jellewie/Arduino-Smart-light/Images/Desk clock hours.jpeg

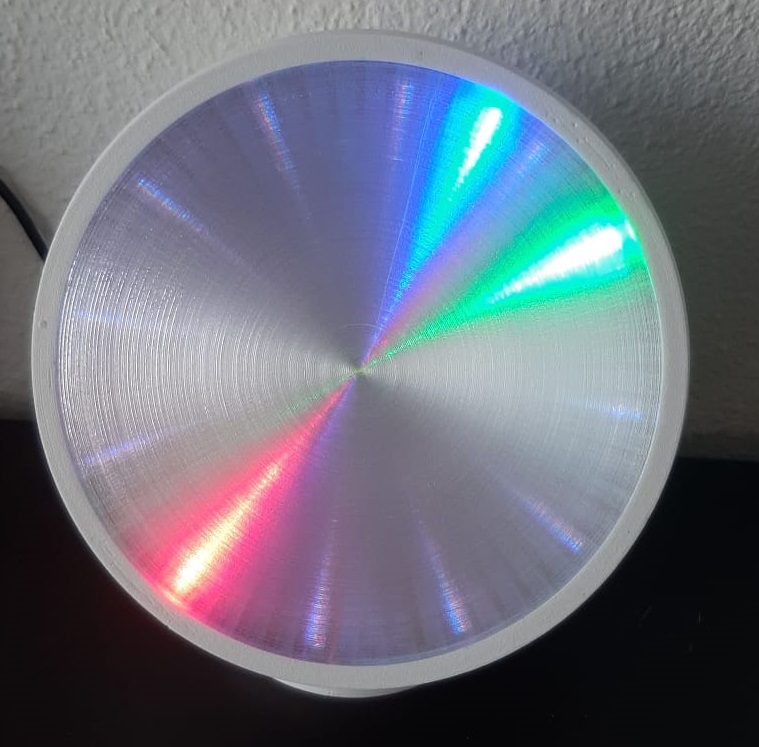
Images/Desk clock hours.jpeg
