jellewie/Arduino-Smart-light/Schematic PCB/V1.3 Desk PCB.png

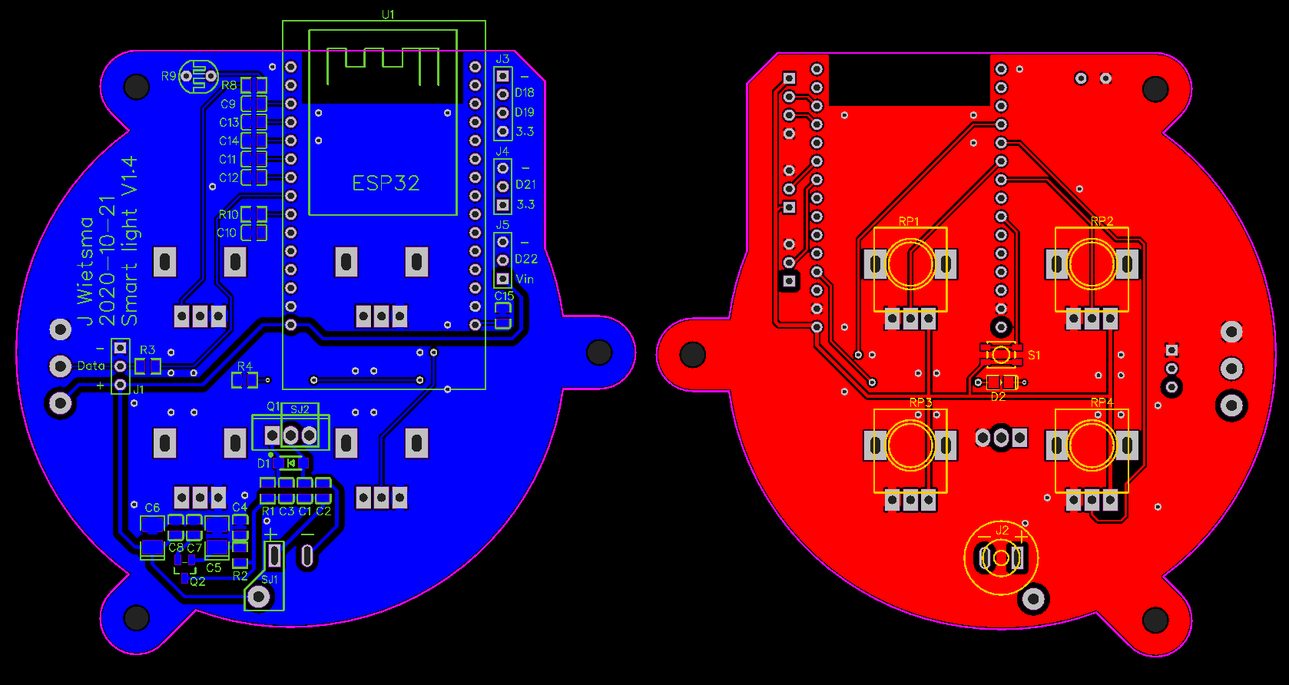
Schematic PCB/V1.3 Desk PCB.png
