jellewie/Arduino-Smart-light/Schematic PCB/V1.3 Schematic.png

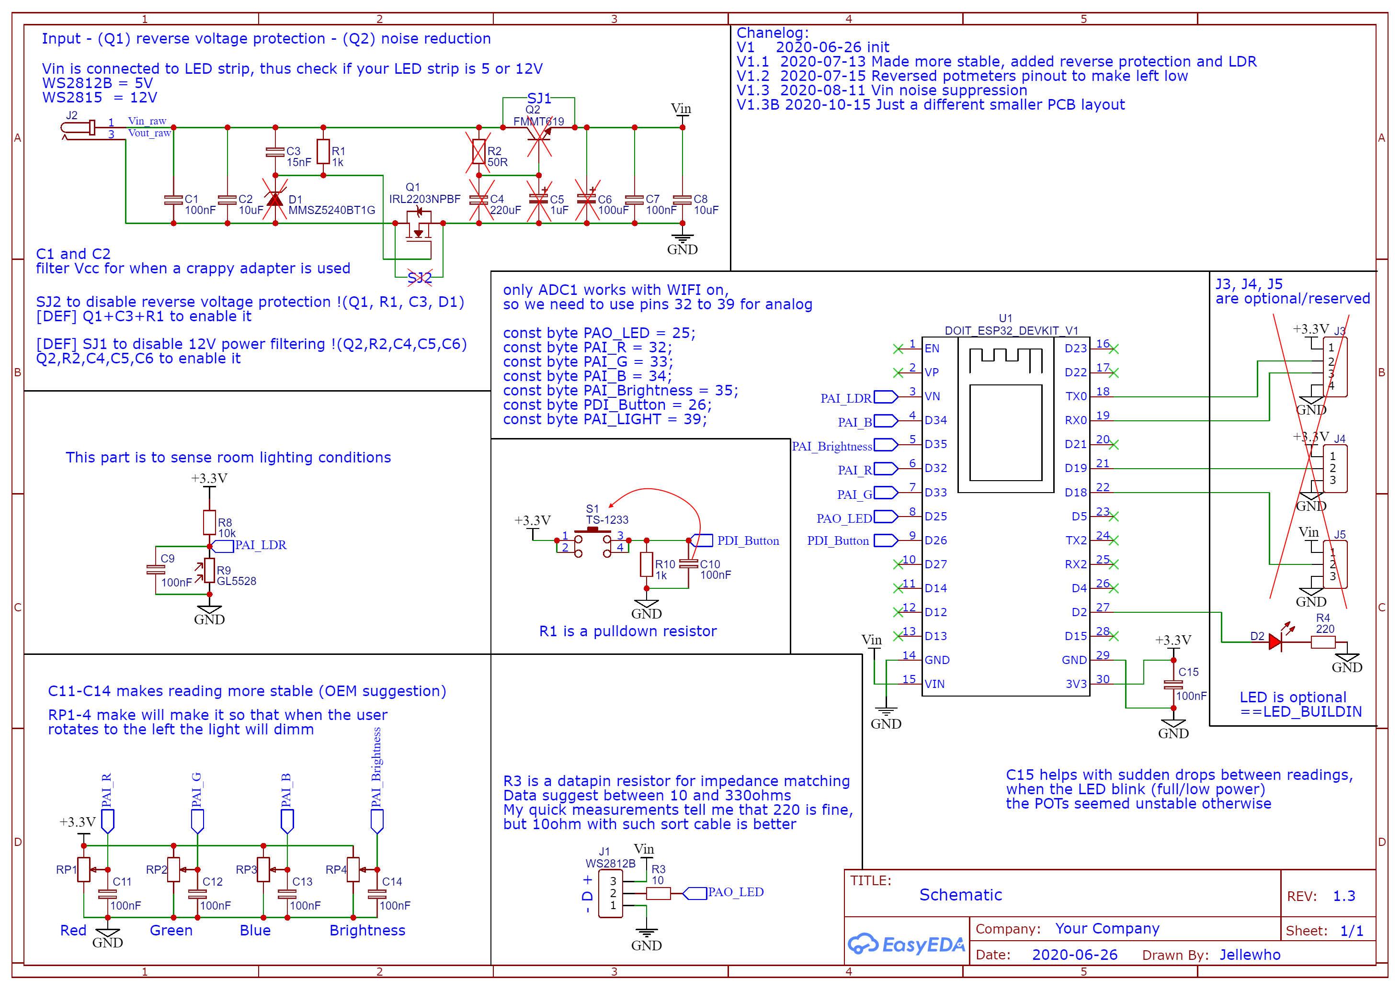
Schematic PCB/V1.3 Schematic.png
