jellewie/Arduino-Smart-light/Arduino/Task.h

/* Written by JelleWho https://github.com/jellewie
  On loop() execute         ExecuteTask()

  HOW TO ADD CUSTOM TASKS
  -"enum xxx"      Add the name to the enum to make the code better to read
  -"TaskString[]"  ^
  -DoTask()        Add what this task does
  -VarCompress()   Add things to compress the 'Var' [Optional but highly suggested)
  -VarDecompress() Add things to decomppress again, requires if Var Compression is used

  Time based tasks will not be auto deleted (execte X at HH:MM:SS)
  Delay based tasks will be auto deleted (execte X in Y ticks)
*/

#define TaskLimit 16                                            //Defined as an byte in for loops, (255 at max), Note this is hooked into WiFimanager EEPROM settings, updating from git after changing this value is NOT recommened
//#define Task_SerialEnabled
#define EEPROMSaveDelayMS 30000                                 //Save to EEPROM in X ms
enum {NONE, SWITCHMODE, DIMMING, BRIGHTEN, RESETESP, CHANGERGB, SAVEEEPROM, SYNCTIME, AUTOBRIGHTNESS, HOURLYANIMATIONS, RANDOMANIMATION}; //Just to make the code easier to read
String TaskString[] = {"NONE", "SWITCHMODE", "DIMMING", "BRIGHTEN", "RESETESP", "CHANGERGB", "SAVEEEPROM", "SYNCTIME", "AUTOBRIGHTNESS", "HOURLYANIMATIONS", "RANDOMANIMATION"}; //ALL CAPS!

const byte Task_Amount = sizeof(ModesString) / sizeof(ModesString[0]); //Why filling this in if we can automate that? :)

//<ip>/task[?PreFix=Value][&....]                               //These are currently HARDCODED into the HTML page, so shouldn't be changed if you want to use the webpage
#define PreFixMode  "o"                                         //1=TASK_ADD, 2=TASK_REMOVE
#define PreFixID    "i"                                         //Task Type (or ID for remove task)
#define PreFixVar   "a"                                         //Task Variable
#define PreFixTimeH "h"                                         //On which time the task needs to be executed
#define PreFixTimeM "m"                                         //^
#define PreFixTimeS "s"                                         //^
#define PreFixTimeT "t"                                         //In howmany ticks the task needs to be executed

struct TASK {
  byte Type = 0;                                                //The ID of the task, these are defined in the enum
  TimeS ExectuteAt = {0, 0, 0, 0};                              //The time in {HH:MM:SS:or millis} to execute this task
  String Var = "";                                              //Used for some special variables
  bool Executed = false;                                        //Just here to keep track of it a Time based task has been executed today
};
TASK TaskList[TaskLimit];
enum {TASK_NOTGIVEN, TASK_ADD, TASK_REMOVE};                    //These are commando's for PreFixMode

//Declare some functions here, so we can cross reference then in the code. Basically just placeholders to the compiler does not whine about that they do not exist yet
extern String ConvertTaskIDToString(byte IN);
extern int    ConvertTaskIDToInt(String IN);
extern void   CutVariable(String _Input, String *_Variable, byte _VariableLength);
extern bool   AddTask(TASK Item, bool _Reversed = false);
//From extern sources
extern bool   UpdateTime();

bool DoTask(TASK Item) {
  bool returnValue = true;
#ifdef Task_SerialEnabled
  Serial.print("TK: DoTask " + ConvertTaskIDToString(Item.Type) + " var=" + String(Item.Var));
  if (Item.ExectuteAt.Ticks > 0)
    Serial.println(" due to Ticks, scheduled for " + String(Item.ExectuteAt.Ticks) + " now=" + String(millis()));
  else
    Serial.println(" due to Time, scheduled for " + String(Item.ExectuteAt.HH) + ":" + String(Item.ExectuteAt.MM) + ":" + String(Item.ExectuteAt.SS));
#endif //Task_SerialEnabled
  switch (Item.Type) {
    case SWITCHMODE: {
        //Var = New Mode
        Mode = ConvertModeToInt(Item.Var);
        UpdateLEDs = true;
      } break;
    case DIMMING: {
        //Var = Stepsize,GoTo,TimeInterfall in ms
        String _Vars[3];
        CutVariable(Item.Var, &_Vars[0], 3);
        byte Stepsize = constrain(_Vars[0].toInt(), 0, 255);
        byte GoTo     = constrain(_Vars[1].toInt(), 0, 255);
        int TimeInterfall       = _Vars[2].toInt();
        byte BRI = FastLED.getBrightness();
        if (BRI - Stepsize < GoTo) {
          BRI = GoTo;
        } else {
          BRI = BRI - Stepsize;
          if (TimeInterfall > 0) {                              //If we need to go further, and need to create another task
            TASK TempTask = Item;
            TempTask.ExectuteAt.Ticks = millis() + TimeInterfall;
            AddTask(TempTask, true);
          }
        }
        FastLED.setBrightness(BRI);
        UpdateLEDs = true;
      } break;
    case BRIGHTEN: {
        //Var = Stepsize,GoTo,TimeInterfall in ms
        String _Vars[3];
        CutVariable(Item.Var, &_Vars[0], 3);
        byte Stepsize = constrain(_Vars[0].toInt(), 0, 255);
        byte GoTo     = constrain(_Vars[1].toInt(), 0, 255);
        int TimeInterfall       = _Vars[2].toInt();
        byte Now = FastLED.getBrightness();
        byte To = 255;
        if (GoTo > 0) To = GoTo;
        if (To - Now < Stepsize) {
          Now = To;
        } else {
          Now += Stepsize;
          if (TimeInterfall > 0) {
            TASK TempTask = Item;
            TempTask.ExectuteAt.Ticks = millis() + TimeInterfall;
            AddTask(TempTask, true);
          }
        }
#ifdef Task_SerialEnabled
        Serial.println("TK: BRIGHTEN from " + String(FastLED.getBrightness()) + " to " + String(Now));
#endif //Task_SerialEnabled
        FastLED.setBrightness(Now);
        UpdateLEDs = true;
      } break;
    case RESETESP: {
        ESP.restart();
      } break;
    case CHANGERGB: {
        //Var = new Red value,new Green value,new Blue value
        String _Vars[4];
        CutVariable(Item.Var, &_Vars[0], 4);
        byte GoToR = constrain(_Vars[0].toInt(), 0, 255);
        byte GoToG = constrain(_Vars[1].toInt(), 0, 255);
        byte GoToB = constrain(_Vars[2].toInt(), 0, 255);
        byte GoToL = constrain(_Vars[3].toInt(), 0, 255);
        Mode = ON;
        LastMode = Mode;
        fill_solid(&(LEDs[0]), TotalLEDs, CRGB(GoToR, GoToG, GoToB));
        if (GoToL != 0)
          FastLED.setBrightness(GoToL);
        UpdateLEDs = true;
      } break;
    case SAVEEEPROM: {
        WiFiManager.WriteEEPROM();
      } break;
    case SYNCTIME: {
        UpdateTime();                                           //Get a new sync timestamp from the server
      } break;
    case AUTOBRIGHTNESS: {
        AutoBrightness = IsTrue(Item.Var);
      } break;
    case HOURLYANIMATIONS: {
        HourlyAnimationS = constrain(Item.Var.toInt(), 0, 255);
      } break;
    case RANDOMANIMATION: {
        //Var = AnimationShowTime where 0=HourlyAnimationS
        int AnimationShowTime = Item.Var.toInt();
        if (AnimationShowTime == 0) AnimationShowTime = HourlyAnimationS;
        StartAnimation(random8(0, TotalAnimations), AnimationShowTime); //Start a random Animation
      } break;
    default:
      returnValue = false;
      break;
  }
  return returnValue;
}
String VarCompress(byte ID, String IN) {
  //Just for compression for EEPROM
#ifdef Convert_SerialEnabled
  Serial.println("CV: VarDecompress '" + String(IN) + "'");
#endif //Convert_SerialEnabled
  IN.replace("\"", "'");                                        //Make sure to change char(") since we can't use that, change to char(')
  IN.replace("\\", "/");                                        //Make sure to change char(\) since we can't use that, change to char(/)
  switch (ID) {
    case NONE: {
        return "";                                              //We do not use it, clear it so save space
      } break;
    case SWITCHMODE: {
        return String(ConvertModeToInt(IN));
      } break;
    //DIMMING
    //BRIGHTEN
    case RESETESP: {
        return "";                                              //We do not use it, clear it so save space
      } break;
    //CHANGERGB
    case SAVEEEPROM: {
        return "";                                              //We do not use it, clear it so save space
      } break;
    case SYNCTIME: {
        return "";                                              //We do not use it, clear it so save space
      } break;
    case AUTOBRIGHTNESS: {
        return String(IsTrue(IN));
      } break;
    case HOURLYANIMATIONS: {
        return String(constrain(IN.toInt(), 0, 32767));
      } break;
    case RANDOMANIMATION: {
        return String(IN.toInt());
      } break;
  }
  return IN;
}
String VarDecompress(byte ID, String IN) {
  //Just for de-compression for EEPROM to show to the user
#ifdef Convert_SerialEnabled
  Serial.println("CV: VarDecompress '" + String(IN) + "'");
#endif //Convert_SerialEnabled
  switch (ID) {
    case SWITCHMODE: {
        return ConvertModeToString(IN.toInt());
      } break;
    case AUTOBRIGHTNESS: {
        return IsTrueToString(IN);
      } break;
  }
  return IN;
}
//==============================
//End of user variables
//==============================
String ConvertTaskIDToString(byte IN) {
#ifdef Convert_SerialEnabled
  Serial.println("CV: ConvertTaskToString '" + String(IN) + "'");
#endif //Convert_SerialEnabled
  if (IN < Task_Amount)
    return TaskString[IN];
  return "UNK";
}
int ConvertTaskIDToInt(String IN) {
#ifdef Convert_SerialEnabled
  Serial.println("CV: ConvertTaskToInt '" + IN + "'");
#endif //Convert_SerialEnabled
  if (StringIsDigit(IN)) {
    if (IN.toInt() <= Task_Amount)
      return IN.toInt();
    else
      return -1;
  }
  IN.toUpperCase();
  for (byte i = 0; i < Task_Amount; i++) {
    if (IN == TaskString[i])
      return i;
  }
  return -1;
}
void CutVariable(String _Input, String *_Variable, byte _VariableLength) {
  //Takes in a string, and cuts them into parts; "test,yes,clock" => {"test","yes","clock"}
  //Returns the output in the same string, for example
  //  String _Output[3], _Input = "test,yes,good,no,what";
  //  CutVariable(_Input, &_Output[0], 3);
  //  Serial.println(String(_Output[0]) + "_" + String(_Output[1]) + "_" + String(_Output[2]));
  byte _StartAt = 0, _WriteTo = 0;
  for (byte i = 0; i <= _Input.length(); i++) {                 //For each character in the input string
    if (_Input.charAt(i) == ',') {
      _Variable[_WriteTo] = _Input.substring(_StartAt, i);
      _WriteTo ++;
      _StartAt = i + 1;
      if (_WriteTo >= _VariableLength - 1) break;               //If last one
    }
  }
  _Variable[_WriteTo] = _Input.substring(_StartAt);
}
bool AddTaskCheck(TASK Item, int i) {
  //Just a private funtion that tries to put the task 'Item' into the slot 'i'
  if (TaskList[i].Type == 0) {                                  //If there is no task
    TaskList[i] = Item;                                         //Save the new task there
    if (TaskList[i].ExectuteAt.HH > TimeCurrent.HH or                                                       //HH+:??:??    in the future due to Hours++
        (TaskList[i].ExectuteAt.HH == TimeCurrent.HH and (                                                  //HH:  AND     if its this hour AND
           TaskList[i].ExectuteAt.MM > TimeCurrent.MM or                                                    //HH:MM+:??     ^this hour AND in the future due to minutes++
           (TaskList[i].ExectuteAt.MM == TimeCurrent.MM and TaskList[i].ExectuteAt.SS > TimeCurrent.SS))))  //HH:MM:SS+     ^this hour AND this minute AND in the future due to seconds++
      TaskList[i].Executed = false;                             //flag this task as not executed
#ifdef Task_SerialEnabled
    Serial.print(" i=" + String(i) + " ID=" + String(Item.Type) + " Var = '" + Item.Var + "'");
    if (Item.ExectuteAt.Ticks > 0) Serial.println(" in " + String(Item.ExectuteAt.Ticks - millis()));
    else Serial.println(" at " + String(Item.ExectuteAt.HH) + ":" + String(Item.ExectuteAt.MM) + ":" + String(Item.ExectuteAt.SS));
#endif //Task_SerialEnabled
    return true;
  }
  return false;
}
bool AddTask(TASK Item, bool _Reversed) {
  //TASK = The task to put into the list
  //Reversed = put the item on the back most of the list instead of in the front, usefull for temp tasks
#ifdef Task_SerialEnabled
  Serial.print("TK: AddTask");
#endif //Task_SerialEnabled
  if (_Reversed) {
    for (int i = TaskLimit; i > 0; i--)                         //For each task that is allowed (start at end and count down)
      if (AddTaskCheck(Item, i)) return true;
  } else {
    for (int i = 0; i < TaskLimit; i++)                         //For each task that is allowed (start at begin and count up)
      if (AddTaskCheck(Item, i)) return true;
  }
#ifdef Task_SerialEnabled
  Serial.println("TaskList full, couldn't add new task");
#endif //Task_SerialEnabled
  return false;
}
bool RemoveTask(byte i) {
  //Remove a task by its nummer in the TaskList
  if (TaskList[i].Type > 0) {                                   //If there is a task
    TaskList[i].Type = 0;                                       //Clear this task entry
#ifdef Task_SerialEnabled
    Serial.println("TK: Removed Task " + String(i));
#endif //Task_SerialEnabled
    return true;                                                //EXIT, task removed
  }
  return false;
}
void RemoveTasksByID(byte ID) {
  //Remove ALL tasks with a sertain ID
  if (ID == 0) return;
  for (byte i = 0; i < TaskLimit; i++) {                        //For each task in the list
    if (TaskList[i].Type == ID) {                               //If there is a task
      TaskList[i].Type = 0;                                     //Clear this task entry
#ifdef Task_SerialEnabled
      Serial.print("TK: RemoveTasksByID " + String(i));
#endif //Task_SerialEnabled
    }
  }
}
void ExecuteTask() {
  for (int i = 0; i < TaskLimit; i++) {                         //For each task in the list
    if (TaskList[i].Type > 0) {                                 //If there is a task
      if (TaskList[i].ExectuteAt.Ticks > 0) {
        if (TaskList[i].ExectuteAt.Ticks <= millis()) {         //If the execute time has pasted
          TASK TempTask = TaskList[i];                          //Create a space to put a new Task in
          RemoveTask(i);                                        //Remove the task, it has been executed
          DoTask(TempTask);                                     //Execute the task entry
        }
      } else if (TimeSet or TaskList[i].Type == SYNCTIME) {
        if (TaskList[i].ExectuteAt.HH != TimeCurrent.HH)        //If we not need to execute the task this hour
          TaskList[i].Executed = false;                         //flag this task as not executed
        else if (!TaskList[i].Executed)                         //If the task has not been executed yet, (and the hour must the the same)
          if (TaskList[i].ExectuteAt.MM < TimeCurrent.MM or//If the minute has passed
              (TaskList[i].ExectuteAt.MM == TimeCurrent.MM and TaskList[i].ExectuteAt.SS <= TimeCurrent.SS)) { //Or its now/in the past
            DoTask(TaskList[i]);                                //Execute this task entry (Do not remove, since TimeTasks (h:m:s) are defined as static)
            TaskList[i].Executed = true;
          }
      }
    }
  }
}
void ScheduleWriteToEEPROM() {
  RemoveTasksByID(SAVEEEPROM);                                  //Remove old EEPROM write command if they exist
  TASK TempTask;
  TempTask.Type = SAVEEEPROM;                                   //Create a new EEPROM write command
  TempTask.ExectuteAt.Ticks = millis() + EEPROMSaveDelayMS;     //Schedule to write data to EEPROM
  if (not(AddTask(TempTask, true)))                             //Add the command to the task list
    DoTask(TempTask);                                           //If the command could not be added to the list, run it now
}
void Tasks_handle_Settings() {
  String ERRORMSG = "";
  byte TaskCommand = 0;
  if (server.args() > 0) {                                      //If manual time given
    TASK TempTask;
    TempTask.Type = 255;                                        //Used to store ID when adding, and i (number in list) for removeal
    TempTask.ExectuteAt.HH = 255;
    TempTask.ExectuteAt.MM = 255;
    TempTask.ExectuteAt.SS = 255;
    TempTask.ExectuteAt.Ticks = 0;
    for (int i = 0; i < server.args(); i++) {
      String ArguName = server.argName(i);
      ArguName.toLowerCase();
      String ArgValue = server.arg(i);
      if (ArgValue != "") {
        if (ArguName == PreFixMode)         TaskCommand = ArgValue.toInt();
        else if (ArguName == PreFixID)      TempTask.Type = ConvertTaskIDToInt(ArgValue);
        else if (ArguName == PreFixVar)     TempTask.Var = ArgValue;
        else if (ArguName == PreFixTimeH)   TempTask.ExectuteAt.HH = ArgValue.toInt() > 23 ? 23 : ArgValue.toInt();
        else if (ArguName == PreFixTimeM)   TempTask.ExectuteAt.MM = ArgValue.toInt() > 59 ? 59 : ArgValue.toInt();
        else if (ArguName == PreFixTimeS)   TempTask.ExectuteAt.SS = ArgValue.toInt() > 59 ? 59 : ArgValue.toInt();
        else if (ArguName == PreFixTimeT)   TempTask.ExectuteAt.Ticks = ArgValue.toInt();
        else                                ERRORMSG += "Unknown arg '" + ArguName + "' with value '" + ArgValue + "'\n";
      }
    }
    if (TempTask.Type == 255) {
      ERRORMSG += "No Task Type/ID given\n";
    } else {
      switch (TaskCommand) {
        case TASK_NOTGIVEN:
          ERRORMSG += "No command given\n";
          break;
        case TASK_ADD: {
            if (TempTask.ExectuteAt.Ticks == 0 and TempTask.ExectuteAt.HH > 24 and TempTask.ExectuteAt.MM > 60 and TempTask.ExectuteAt.SS > 60) {
              ERRORMSG += "No (proper) Task time given\n";
            } else {
              if (TempTask.ExectuteAt.Ticks != 0) {             //If we have a delay, not a alarm based on time
                TempTask.ExectuteAt.Ticks += millis();          //Set the delay to be relative from now
                TempTask.ExectuteAt.HH = 0;                     //Reset the time, we dont use these
                TempTask.ExectuteAt.MM = 0;
                TempTask.ExectuteAt.SS = 0;
              } else {
                if (!TimeSet)
                  ERRORMSG += "Warning time is not synced\n";
                if (TempTask.ExectuteAt.HH > 24) TempTask.ExectuteAt.HH = 0;
                if (TempTask.ExectuteAt.MM > 60) TempTask.ExectuteAt.MM = 0;
                if (TempTask.ExectuteAt.SS > 60) TempTask.ExectuteAt.SS = 0;
              }
              TempTask.Var = VarCompress(TempTask.Type, TempTask.Var);
              if (AddTask(TempTask)) {
                if (TempTask.ExectuteAt.Ticks == 0)             //If it is a time event (HH:MM:SS)
                  ScheduleWriteToEEPROM();                      //Schedule to save the changes to EEPROM
                ERRORMSG += "Could not save tasklist\n";
              } else
                ERRORMSG += "Could not add tasks\n";
            }
            break;
          }
        case TASK_REMOVE: { //Remove
            byte i = TempTask.Type;
            byte TaskID = TaskList[i].Type;
            if (RemoveTask(i)) {
              if (i < 8 and TaskID != SAVEEEPROM and TaskID != RESETESP)//If this Task was (should) saved to EEPROM, and was not a SAVEEEPROM task
                ScheduleWriteToEEPROM();                        //Schedule to save the changes to EEPROM
            } else
              ERRORMSG += "Could not find task " + String(TempTask.Type) + " in the tasklist\n";
            break;
          }
      }
    }
  }
  if (ERRORMSG != "")
    server.send(400, "text/plain", ERRORMSG);
  else {
    switch (TaskCommand) {
      case TASK_ADD:    server.send(200, "text/plain", "Task added");     break;
      case TASK_REMOVE: server.send(200, "text/plain", "Task removed");   break;
      default:          server.send(200, "text/plain", "OK");             break;
    }
  }
#ifdef Server_SerialEnabled
  Serial.println("SV: 200/400 Tasks_Settings " + ERRORMSG);
#endif //Server_SerialEnabled
}
void Tasks_handle_GetTasks() {
  String ans;
  for (byte i = 0; i < TaskLimit; i++) {                        //For each task in the list
    if (TaskList[i].Type > 0) {                                 //If there is a task
      if (ans != "") ans += ",";
      ans += "{\"id\":" + String(i) + ","
             "\"type\":\"" + ConvertTaskIDToString(TaskList[i].Type) + "\","
             "\"var\":\"" + VarDecompress(TaskList[i].Type, TaskList[i].Var) + "\",";
      if (TaskList[i].ExectuteAt.Ticks > 0)
        ans += "\"timeFromNow\":" + String(TaskList[i].ExectuteAt.Ticks - millis());
      else
        ans += "\"time\":\"" + String(TaskList[i].ExectuteAt.HH) + ":" + String(TaskList[i].ExectuteAt.MM) + ":" + String(TaskList[i].ExectuteAt.SS) + "\"";
      ans += "}";
    }
  }
  ans = "{\"tasks\":[" + ans + "],\"currentTime\":[" + String(TimeCurrent.HH) + "," + String(TimeCurrent.MM) + "," + String(TimeCurrent.SS) + "]}";
  server.send(200, "application/json", ans);
#ifdef Server_SerialEnabled
  Serial.println("SV: 200 Getcolors " + ans);
#endif //Server_SerialEnabled
}
